socketwench/rc2014-psu-case/keystone/main.scad

include <keystone.scad>

Select = 0; // [0:keystoneCutout, 1:keystonePort]

if (Select==0) {
    keystoneCutout();
} else if (Select==1) {
    keystonePort();
}
